jdbrinton/bigpine-remote-camera/fw/include/ov2640.h

#ifndef OV2640_REGS_H
#define OV2640_REGS_H

#define OV2640_7BIT_ADDR 	0x30

void ov2640_init();
uint32_t ov2640_capture(char** buf_in);

struct sensor_reg {
	uint16_t reg;
	uint16_t val;
};

const struct sensor_reg OV2640_JPEG_INIT[] =
{
  { 0xff, 0x00 },
  { 0x2c, 0xff },
  { 0x2e, 0xdf },
  { 0xff, 0x01 },
  { 0x3c, 0x32 },
  { 0x11, 0x00 },	
  { 0x09, 0x02 },
  { 0x04, 0x28 },
  { 0x13, 0xe5 },
  { 0x14, 0x48 },
  { 0x2c, 0x0c },
  { 0x33, 0x78 },
  { 0x3a, 0x33 },
  { 0x3b, 0xfB },
  { 0x3e, 0x00 },
  { 0x43, 0x11 },
  { 0x16, 0x10 },
  { 0x39, 0x92 },
  { 0x35, 0xda },
  { 0x22, 0x1a },
  { 0x37, 0xc3 },
  { 0x23, 0x00 },
  { 0x34, 0xc0 },
  { 0x36, 0x1a },
  { 0x06, 0x88 },
  { 0x07, 0xc0 },
  { 0x0d, 0x87 },
  { 0x0e, 0x41 },
  { 0x4c, 0x00 },
  { 0x48, 0x00 },
  { 0x5B, 0x00 },
  { 0x42, 0x03 },
  { 0x4a, 0x81 },
  { 0x21, 0x99 },
  { 0x24, 0x40 },
  { 0x25, 0x38 },
  { 0x26, 0x82 },
  { 0x5c, 0x00 },
  { 0x63, 0x00 },
  { 0x61, 0x70 },
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
               
  { 0x12, 0x40 },
  { 0xd3, 0x04 },	//{ 0xd3, 0x7f },
  { 0xc0, 0x16 },
  { 0xC1, 0x12 },
  { 0x8c, 0x00 },
  { 0x86, 0x3d },
  { 0x50, 0x00 },
  { 0x51, 0x2C },
  { 0x52, 0x24 },
  { 0x53, 0x00 },
  { 0x54, 0x00 },
  { 0x55, 0x00 },
  { 0x5A, 0x2c },
  { 0x5b, 0x24 },
  { 0x5c, 0x00 },
  { 0xff, 0xff },
};             

const struct sensor_reg OV2640_YUV422[] =
{
  { 0xFF, 0x00 },
  { 0x05, 0x00 },
  { 0xDA, 0x10 },
  { 0xD7, 0x03 },
  { 0xDF, 0x00 },
  { 0x33, 0x80 },
  { 0x3C, 0x40 },
  { 0xe1, 0x77 },
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
  { 0xe0, 0x04 },
  { 0xc0, 0x64 },
  { 0xc1, 0x4b },
  { 0x86, 0x35 },
  { 0x50, 0x89 },
  { 0x51, 0xc8 },
  { 0x52, 0x96 },
  { 0x53, 0x00 },
  { 0x54, 0x00 },
  { 0x55, 0x00 },
  { 0x57, 0x00 },
  { 0x5a, 0x50 },
  { 0x5b, 0x3c },
  { 0x5c, 0x00 },
  { 0xe0, 0x00 },
  { 0xff, 0xff },
};

   /* JPG 1600x1200 */
const struct sensor_reg OV2640_1600x1200_JPEG[] =  
{
	{0xff, 0x01},
	{0x11, 0x01},
	{0x12, 0x00}, // Bit[6:4]: Resolution selection
	{0x17, 0x11}, // HREFST[10:3]
	{0x18, 0x75}, // HREFEND[10:3]
	{0x32, 0x36}, // Bit[5:3]: HREFEND[2:0]; Bit[2:0]: HREFST[2:0]
	{0x19, 0x01}, // VSTRT[9:2]
	{0x1a, 0x97}, // VEND[9:2]
	{0x03, 0x0f}, // Bit[3:2]: VEND[1:0]; Bit[1:0]: VSTRT[1:0]
	{0x37, 0x40},
	{0x4f, 0xbb},
	{0x50, 0x9c},
	{0x5a, 0x57},
	{0x6d, 0x80},
	{0x3d, 0x34},
	{0x39, 0x02},
	{0x35, 0x88},
	{0x22, 0x0a},
	{0x37, 0x40},
	{0x34, 0xa0},
	{0x06, 0x02},
	{0x0d, 0xb7},
	{0x0e, 0x01},
	
	{0xff, 0x00},        	                              
	{0xe0, 0x04},                                   
	{0xc0, 0xc8},                                   
	{0xc1, 0x96},                                   
	{0x86, 0x3d},                                   
	{0x50, 0x00},                                   
	{0x51, 0x90},                                   
	{0x52, 0x2c},                                   
	{0x53, 0x00},                                   
	{0x54, 0x00},                                   
	{0x55, 0x88},                                   
	{0x57, 0x00},                                   
	{0x5a, 0x90},                                   
	{0x5b, 0x2C},                                   
	{0x5c, 0x05},              //bit2->1;bit[1:0]->1
	{0xd3, 0x02},                                   
	{0xe0, 0x00},                                   
                      
  	{0xff, 0xff},
};

/****************************************************/
/* ArduChip registers definition 											*/
/****************************************************/
#define RWBIT					0x80  //READ AND WRITE BIT IS BIT[7]

#define ARDUCHIP_TEST1       	0x00  //TEST register

#define ARDUCHIP_MODE      		0x02  //Mode register
#define MCU2LCD_MODE       		0x00
#define CAM2LCD_MODE       		0x01
#define LCD2MCU_MODE       		0x02

#define ARDUCHIP_TIM       		0x03  //Timming control

#define ARDUCHIP_FIFO      		0x04  //FIFO and I2C control
#define FIFO_CLEAR_MASK    		0x01
#define FIFO_START_MASK    		0x02
#define FIFO_RDPTR_RST_MASK     0x10
#define FIFO_WRPTR_RST_MASK     0x20

#define ARDUCHIP_GPIO			0x06  //GPIO Write Register
#define GPIO_RESET_MASK			0x01  //0 = Sensor reset,				1 =  Sensor normal operation
#define GPIO_PWDN_MASK			0x02  //0 = Sensor normal operation, 	1 = Sensor standby
#define GPIO_PWREN_MASK			0x04  //0 = Sensor LDO disable, 		1 = sensor LDO enable

#define BURST_FIFO_READ			0x3C  //Burst FIFO read operation
#define SINGLE_FIFO_READ		0x3D  //Single FIFO read operation

#define ARDUCHIP_REV       		0x40  //ArduCHIP revision
#define VER_LOW_MASK       		0x3F
#define VER_HIGH_MASK      		0xC0

#define ARDUCHIP_TRIG      		0x41  //Trigger source
#define VSYNC_MASK         		0x01
#define SHUTTER_MASK       		0x02
#define CAP_DONE_MASK      		0x08

#define FIFO_SIZE1				0x42  //Camera write FIFO size[7:0] for burst to read
#define FIFO_SIZE2				0x43  //Camera write FIFO size[15:8]
#define FIFO_SIZE3				0x44  //Camera write FIFO size[18:16]

#endif
