jdbrinton/bigpine-remote-camera/fw/src/base64_encode.cpp

#include "base64_encode.h"
#include "mbed.h"

#include <stdlib.h>

extern RawSerial *g_console_uart;

static char encoding_table[] = {'A', 'B', 'C', 'D', 'E', 'F', 'G', 'H',
                                'I', 'J', 'K', 'L', 'M', 'N', 'O', 'P',
                                'Q', 'R', 'S', 'T', 'U', 'V', 'W', 'X',
                                'Y', 'Z', 'a', 'b', 'c', 'd', 'e', 'f',
                                'g', 'h', 'i', 'j', 'k', 'l', 'm', 'n',
                                'o', 'p', 'q', 'r', 's', 't', 'u', 'v',
                                'w', 'x', 'y', 'z', '0', '1', '2', '3',
                                '4', '5', '6', '7', '8', '9', '+', '/'};
static char *decoding_table = NULL;
static int mod_table[] = {0, 2, 1};


void base64_encode(char* out, const char *data, uint32_t input_length)
{
    uint32_t idx = 0;
    for (int i = 0; i < input_length;) {

        uint32_t octet_a = i < input_length ? (unsigned char)data[i++] : 0;
        uint32_t octet_b = i < input_length ? (unsigned char)data[i++] : 0;
        uint32_t octet_c = i < input_length ? (unsigned char)data[i++] : 0;

        uint32_t triple = (octet_a << 0x10) + (octet_b << 0x08) + octet_c;

        out[idx++] = encoding_table[(triple >> 3 * 6) & 0x3F];
        out[idx++] = encoding_table[(triple >> 2 * 6) & 0x3F];
        out[idx++] = encoding_table[(triple >> 1 * 6) & 0x3F];
        out[idx++] = encoding_table[(triple >> 0 * 6) & 0x3F];
    }

    for (int i = 0; i < mod_table[input_length % 3]; i++)
        out[idx++] = '=';
}
